magmalag/V-Rod-Custom-Fuel-Level-Sensor/photos/IMG_20260529_173331.jpg

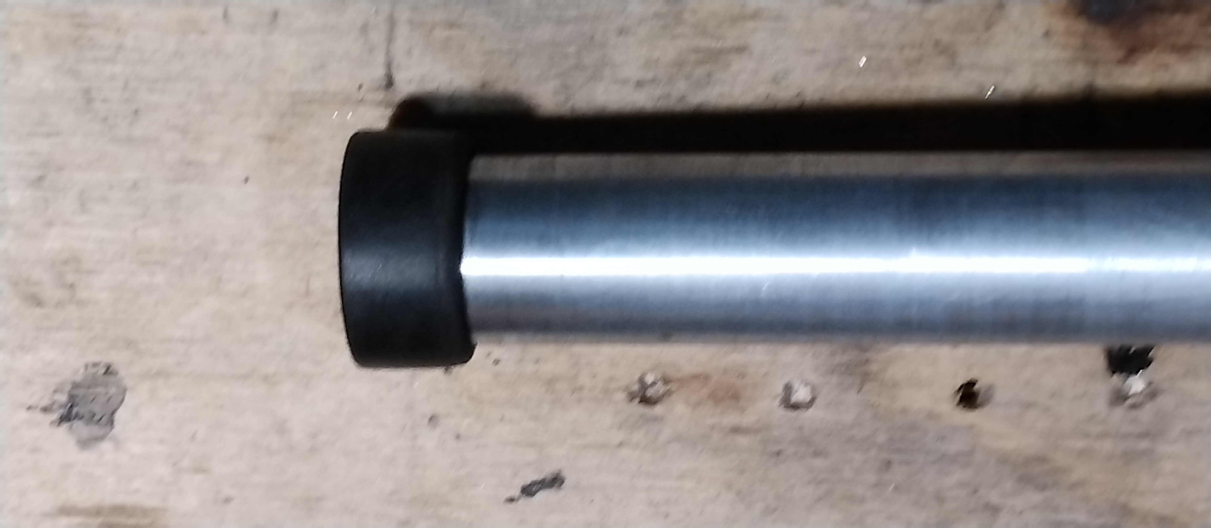
photos/IMG_20260529_173331.jpg
